mattstock/cococpld/firmware/debug.cpp

#include <Arduino.h>
#include <SD.h>
#include "busio.h"
#include "rom.h"
#include "debug.h"
#include "firmware2.h"
#include "fdc.h"

char cmd[30];

void readLine() {
  int index = 0;
  while (1) {
    if (Serial.available() > 0) {
      cmd[index] = Serial.read();
      cmd[index+1] = '\0';
      Serial.write(&(cmd[index]));
      if (cmd[index] == 0x0b) {
	index = 0;
      } else if (cmd[index] == '\b') {
        if (index != 0)
	  index--;
      } else if (cmd[index] == '\r') {
	Serial.println("");
	cmd[index] = '\0';
	index = 0;
	return;
      } else
	index++;
    } 
  }
}

char a2h(char c) {
  if (c < 'a')
    return c-48;
  else
    return c-97+10;
}

void debugCommand() {
  Serial.print("BEXKAT> ");
  readLine();
  switch (cmd[0]) {
  case 'r':
    if (cmd[1] == 's')
      Serial.println(readStatus(), HEX);
    else
      Serial.println(readData(), HEX);
    break;
  case 'w':
    setData((a2h(cmd[1]) << 4) + a2h(cmd[2]));
    Serial.println("Data written");
    break;
  case 'd':
    switch (cmd[1]) {
    case '0':
      setBank(0);
      programROM(SD.open(config[ROM0]));
      break;
    case '1':
      setBank(1);
      programROM(SD.open(config[ROM1]));
      break;
    case '2':
      setBank(2);
      programROM(SD.open(config[ROM2]));
      break;
    case '3':
      setBank(3);
      programROM(SD.open(config[ROM3]));
      break;
    }
    Serial.println("Flash programmed");
    break;
  case 'v':
    switch (cmd[1]) {
    case '0':
      setBank(0);
      verifyROM(SD.open(config[ROM0]));
      break;
    case '1':
      setBank(1);
      verifyROM(SD.open(config[ROM1]));
      break;
    case '2':
      setBank(2);
      verifyROM(SD.open(config[ROM2]));
      break;
    case '3':
      setBank(3);
      verifyROM(SD.open(config[ROM3]));
      break;
    }
    Serial.println("Flash verify");
    break;
  case 'f':
    Serial.println("Peripheral mode");
    controlPending = false;
    commandPending = false;
    attachInterrupt(0, loadConfig, FALLING);
    attachInterrupt(1, loadCommand, FALLING);
    fdc();
    break;
  case 'e':
    eraseFlash();
    Serial.println("FLASH erased");
    break;
  case 'i':
    controlPending = false;
    commandPending = false;
    attachInterrupt(0, loadConfig, FALLING);
    attachInterrupt(1, loadCommand, FALLING);
    Serial.println("interrupts enabled");
    break;
  case 'a':
    setAddress((a2h(cmd[1]) << 12) + (a2h(cmd[2]) << 8) +
	       (a2h(cmd[3]) << 4) + a2h(cmd[4]));
    Serial.println("Address set");
    break;
  case 'b':
    setBank(atoi((const char *)cmd[1]));
    break;
  case 'h':
    wakeCoco();
    break;
  }
}

void fault() {
  // error blinky
  while (1) {
    digitalWrite(LED_PIN, HIGH);
    delay(1000);
    digitalWrite(LED_PIN, LOW);
    delay(1000);
  }
}
